UniOfGreenwich/ace-2023_-ace_2023_team-1/research_folder/Images/asus_csb_motherboard_image.png

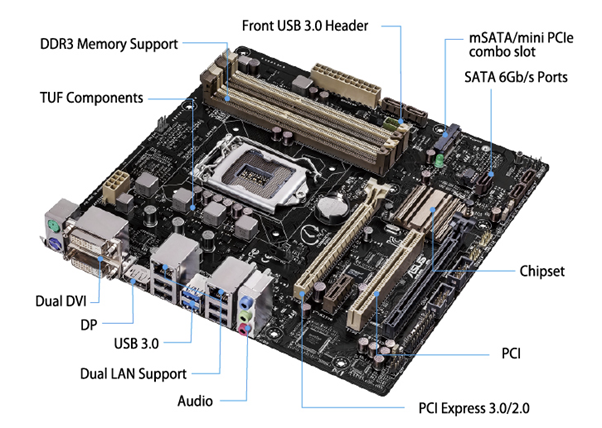
research_folder/Images/asus_csb_motherboard_image.png
