UniOfGreenwich/ace-2023_-ace_2023_team-1/research_folder/Images/intel_core_i5-4590_cpu.jpg

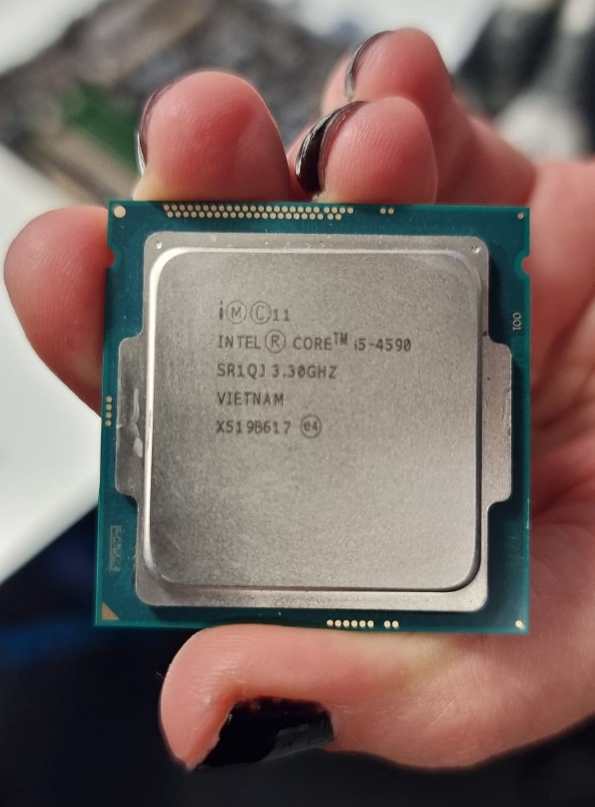
research_folder/Images/intel_core_i5-4590_cpu.jpg
