UniOfGreenwich/ace-2023_-ace_2023_team-1/research_folder/Images/lsblk.jpeg

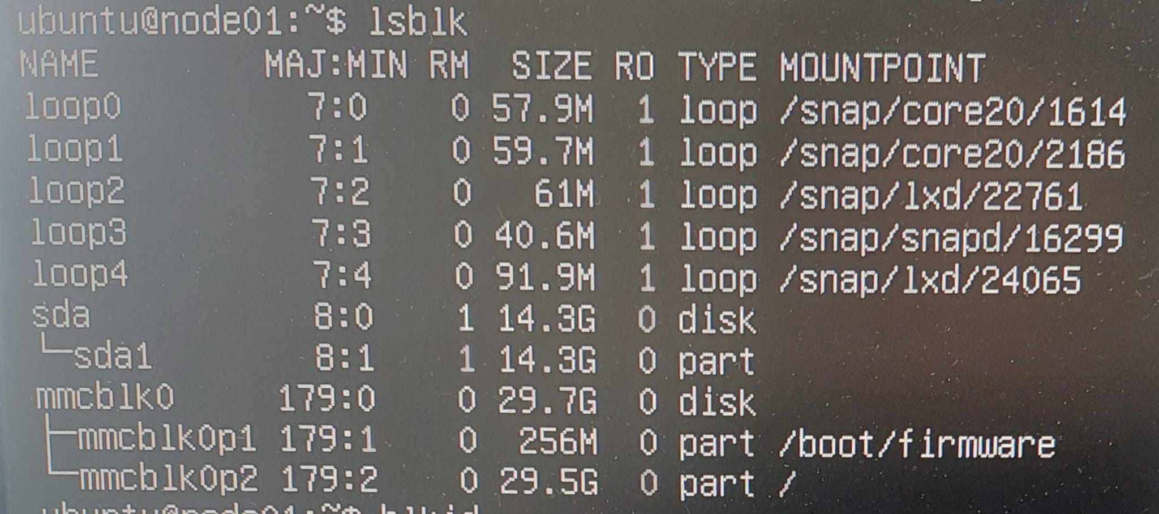
research_folder/Images/lsblk.jpeg
