UniOfGreenwich/ace-2023_-ace_2023_team-1/research_folder/Images/PSU750W2.jpeg

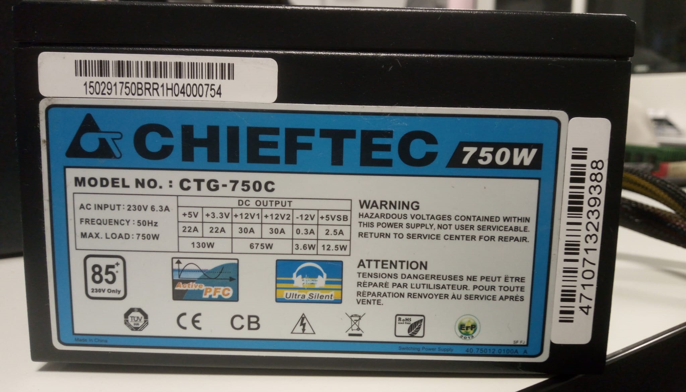
research_folder/Images/PSU750W2.jpeg
