UniOfGreenwich/ace-2023_-ace_2023_team-1/research_folder/Images/ScreenshotAsus.png

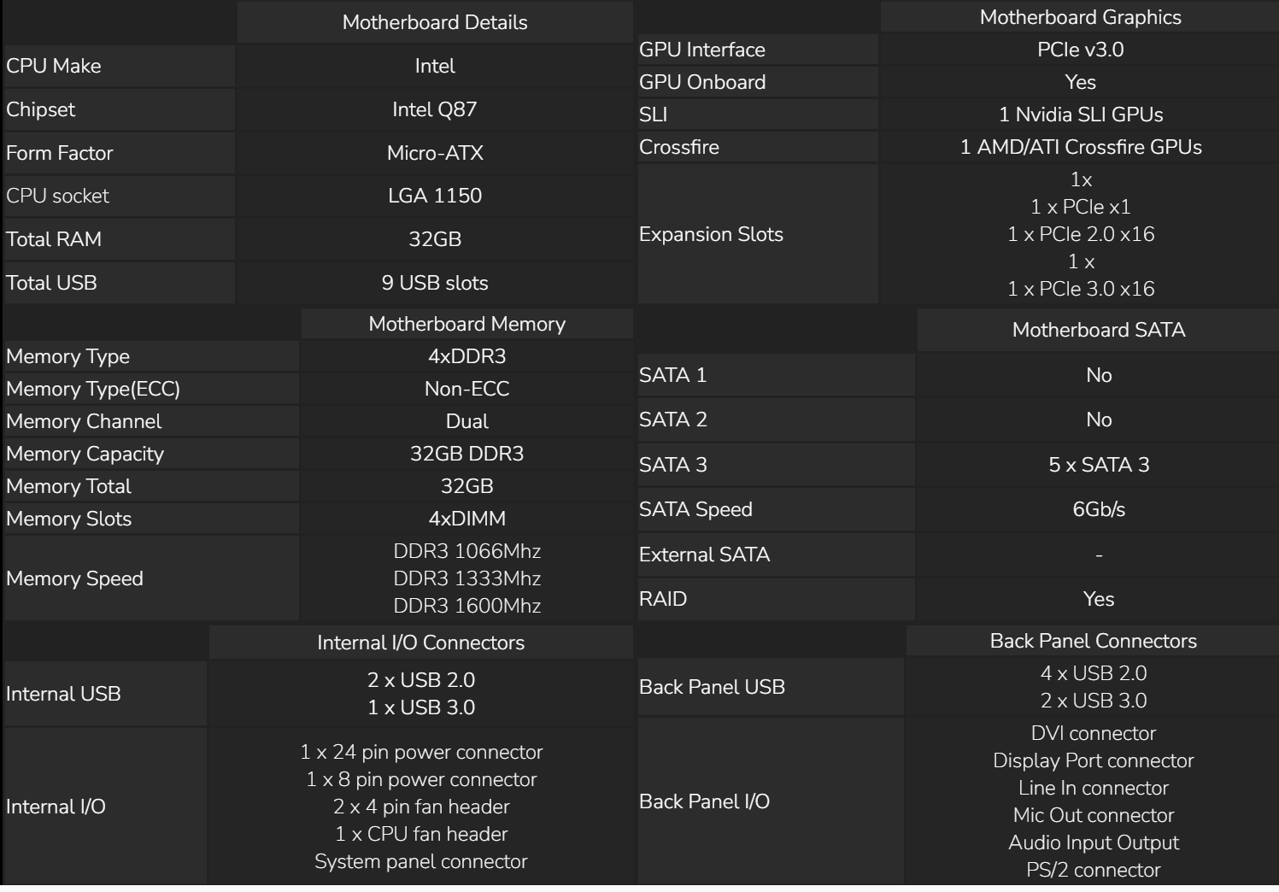
research_folder/Images/ScreenshotAsus.png
