UniOfGreenwich/ace-2023_-ace_2023_team-1/research_folder/Images/SSDback.jpeg

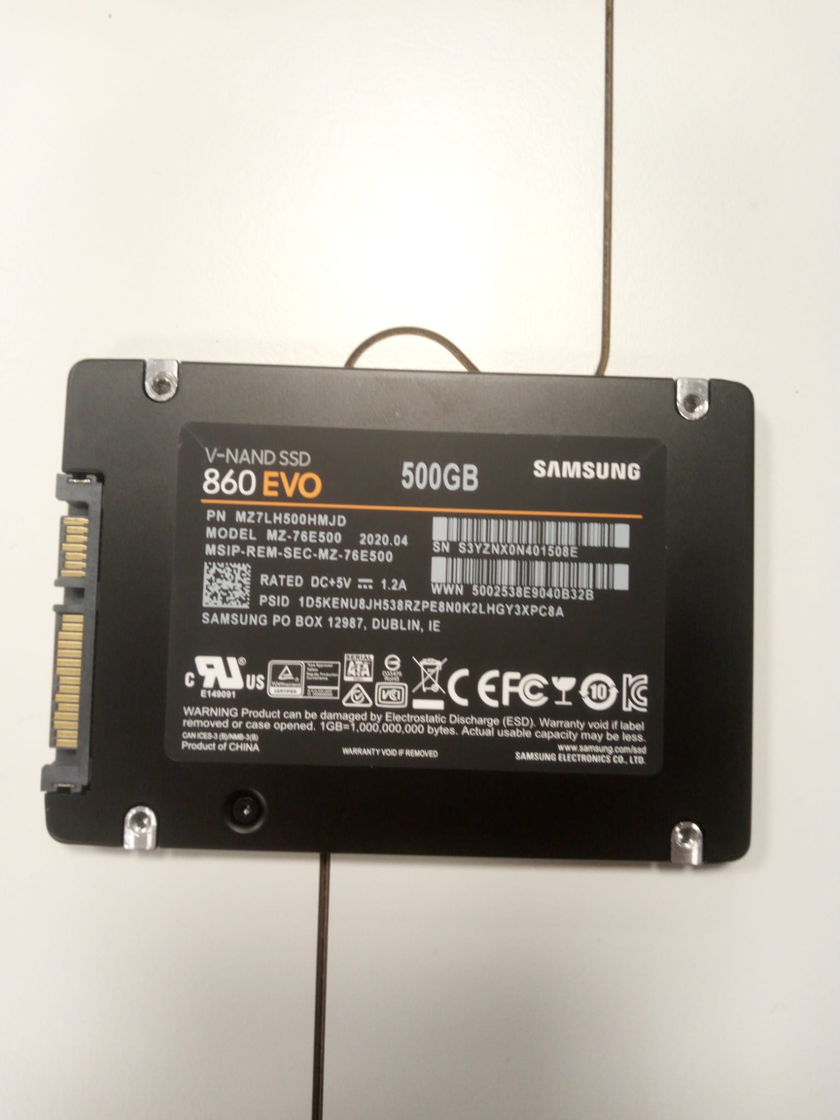
research_folder/Images/SSDback.jpeg
