UniOfGreenwich/ace-2023_-ace_2023_team-1/hpc_case_design/laser_cutting/dxf_files/inner_shelf/inner_shelf_right.dxf

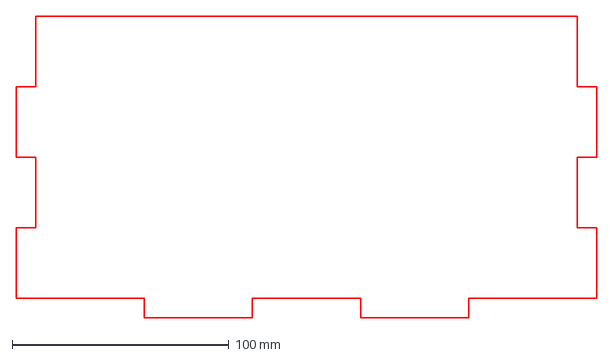
[picture p38: CAD file, 2024-04-01]
hpc_case_design/laser_cutting/dxf_files/inner_shelf/inner_shelf_right.dxf
268.0 x 139.0 mm
