UniOfGreenwich/ace-2023_-ace_2023_team-1/hpc_case_design/laser_cutting/dxf_files/outer_shelf/outer_layer_b.dxf

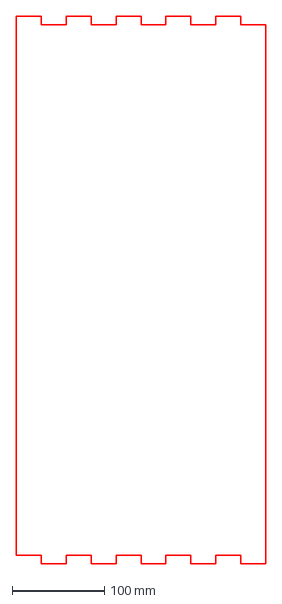
[picture p39: CAD file, 2024-04-01]
hpc_case_design/laser_cutting/dxf_files/outer_shelf/outer_layer_b.dxf
270.0 x 593.0 mm
