UniOfGreenwich/ace-2023_-ace_2023_team-1/hpc_case_design/3d_printing/stl_files/head-shelf/switch_bottom.stl

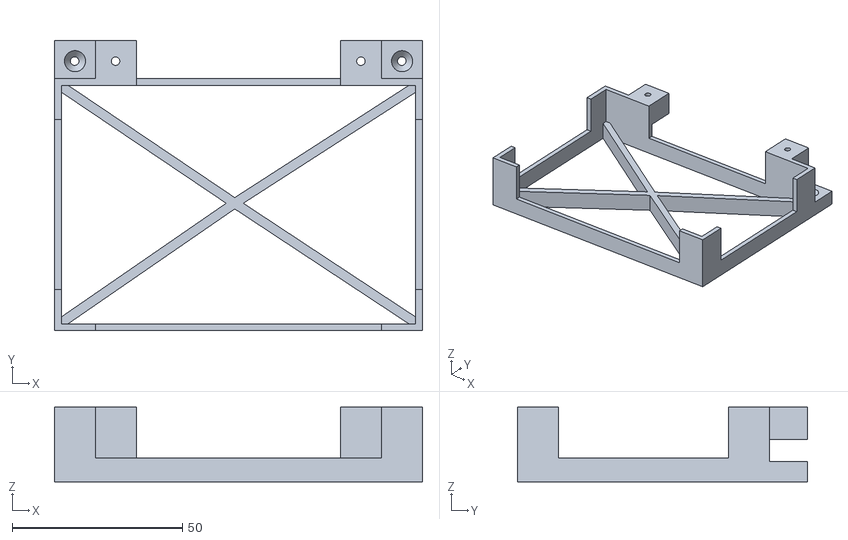
[picture p41: CAD file, 2024-04-01]
hpc_case_design/3d_printing/stl_files/head-shelf/switch_bottom.stl
108.0 x 85.2 x 22.0
