UniOfGreenwich/ace-2023_-ace_2023_team-1/hpc_case_design/laser_cutting/dxf_files/inner_shelf/inner_shelf_bottom.dxf

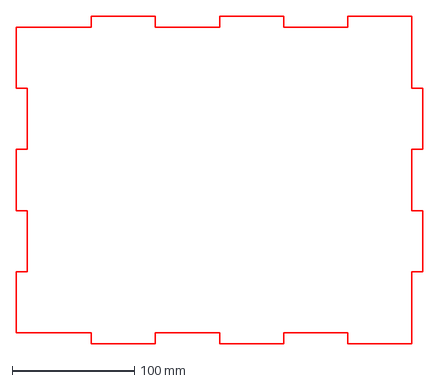
[picture p44: CAD file, 2024-04-01]
hpc_case_design/laser_cutting/dxf_files/inner_shelf/inner_shelf_bottom.dxf
333.0 x 268.0 mm
