UniOfGreenwich/ace-2023_-ace_2023_team-1/hpc_case_design/3d_printing/stl_files/general-shelf/top_wall_handle.stl

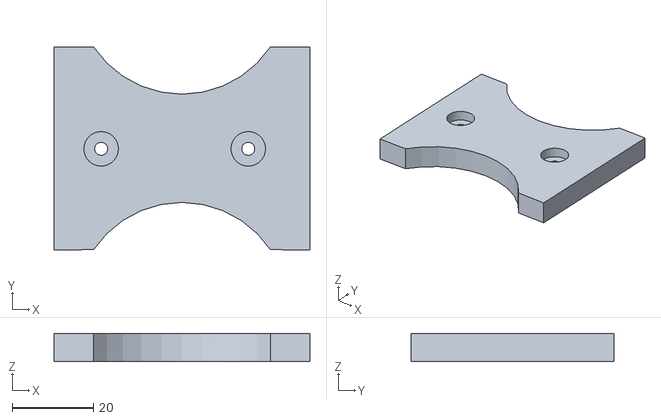
[picture p48: CAD file, 2024-04-01]
hpc_case_design/3d_printing/stl_files/general-shelf/top_wall_handle.stl
63.0 x 50.0 x 7.00
