UniOfGreenwich/ace-2023_-ace_2023_team-1/hpc_case_design/3d_printing/stl_files/general-shelf/bracket_3.stl

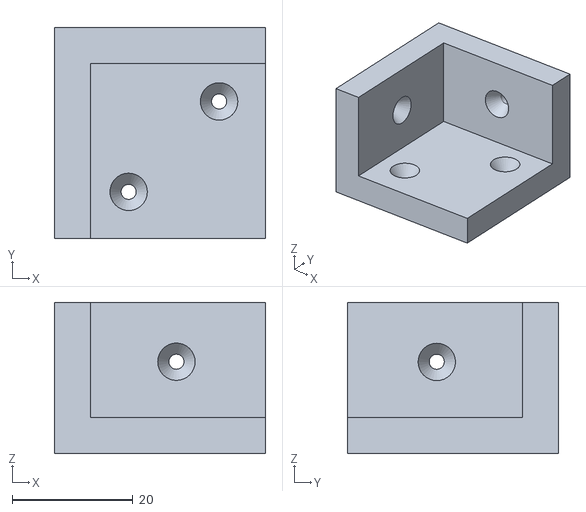
[picture p49: CAD file, 2024-04-01]
hpc_case_design/3d_printing/stl_files/general-shelf/bracket_3.stl
35.0 x 35.0 x 25.0
