UniOfGreenwich/ace-2023_-ace_2023_team-1/hpc_case_design/3d_printing/cad_files/renders/render_4.png

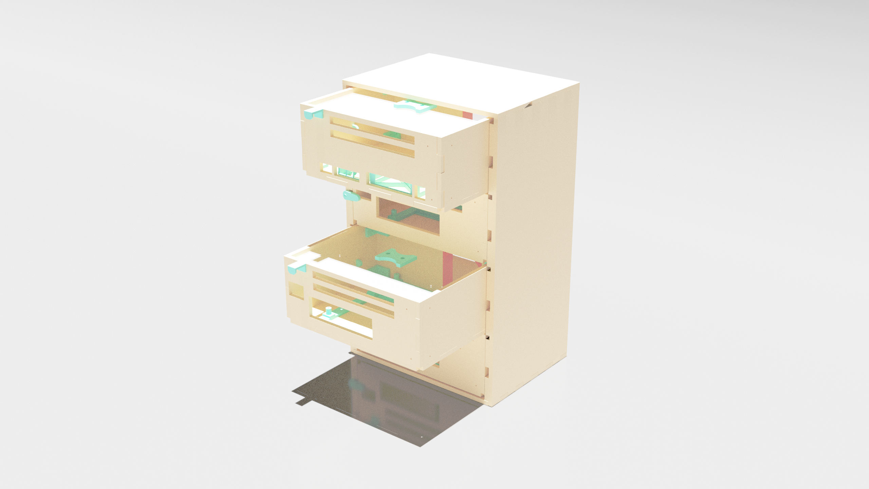
hpc_case_design/3d_printing/cad_files/renders/render_4.png
